imflawlezz/tty-buddy/hardware/schematics/tty-buddy/tty-buddy.kicad_sch

## KiCad design hardware/schematics/tty-buddy/tty-buddy.kicad_sch (2026-09-05)

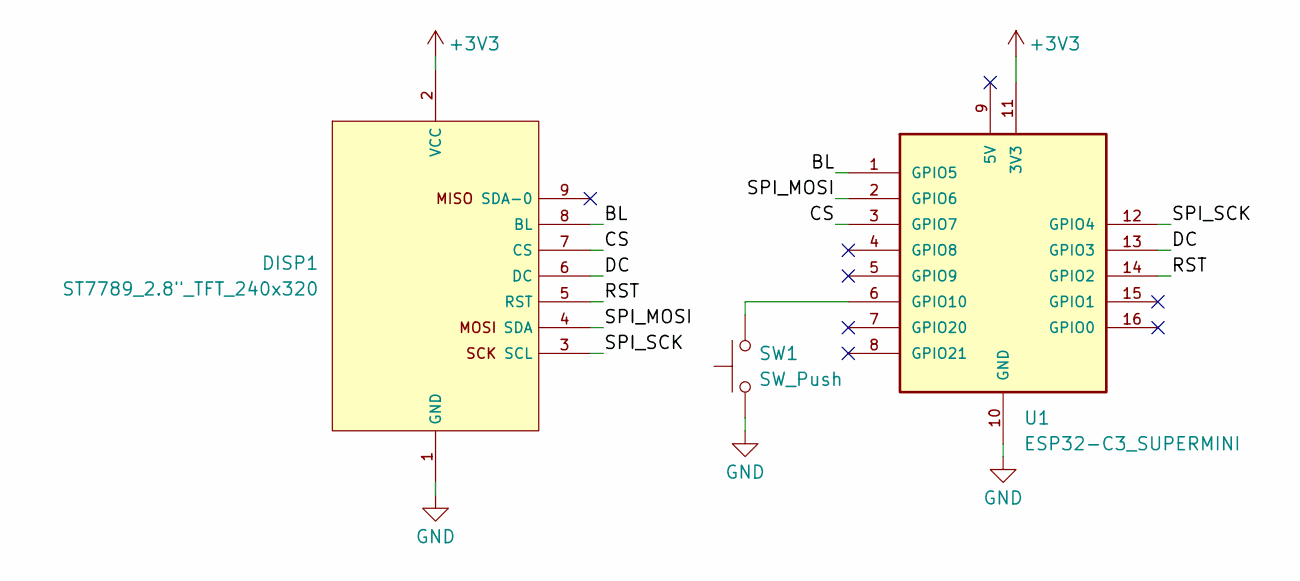
[picture p5: schematic tty-buddy.kicad_sch]

Parts:
DISP1: ST7789_2.8"_TFT_240x320
SW1: SW_Push
U1: ESP32-C3_SUPERMINI

Connections:
+3V3: DISP1.2 (VCC), U1.11 (3V3)
BL: DISP1.8 (BL), U1.1 (GPIO5)
CS: DISP1.7 (CS), U1.3 (GPIO7)
DC: DISP1.6 (DC), U1.13 (GPIO3)
GND: DISP1.1 (GND), SW1.1, U1.10 (GND)
unnamed: SW1.2, U1.6 (GPIO10)
RST: DISP1.5 (RST), U1.14 (GPIO2)
SPI_MOSI: DISP1.4 (SDA), U1.2 (GPIO6)
SPI_SCK: DISP1.3 (SCL), U1.12 (GPIO4)
