imflawlezz/tty-buddy/daemon/src/discover.rs

//! USB serial discovery (Linux sysfs + optional saved settings).

use std::fmt;
use std::fs;
use std::path::{Path, PathBuf};

use anyhow::Result;

use crate::settings::DaemonSettings;

pub const ESP_VID: u16 = 0x303A;
pub const ESP_PID_JTAG: u16 = 0x1001;

#[derive(Debug, Clone)]
pub struct SerialDevice {
    pub path: String,
    pub vid: Option<u16>,
    pub pid: Option<u16>,
    pub serial: Option<String>,
    pub product: Option<String>,
    pub manufacturer: Option<String>,
}

impl fmt::Display for SerialDevice {
    fn fmt(&self, f: &mut fmt::Formatter<'_>) -> fmt::Result {
        write!(f, "{}", self.path)?;
        match (self.vid, self.pid) {
            (Some(v), Some(p)) => write!(f, "  {:04x}:{:04x}", v, p)?,
            _ => write!(f, "  ????")?,
        }
        if let Some(ref m) = self.manufacturer {
            write!(f, "  {m}")?;
        }
        if let Some(ref p) = self.product {
            write!(f, "  {p}")?;
        }
        if let Some(ref s) = self.serial {
            write!(f, "  serial={s}")?;
        }
        if self.vid == Some(ESP_VID) {
            write!(f, "  [espressif]")?;
        }
        Ok(())
    }
}

fn read_hex_u16(path: &Path) -> Option<u16> {
    let s = fs::read_to_string(path).ok()?;
    u16::from_str_radix(s.trim(), 16).ok()
}

fn read_trim(path: &Path) -> Option<String> {
    let s = fs::read_to_string(path).ok()?;
    let t = s.trim().to_string();
    if t.is_empty() {
        None
    } else {
        Some(t)
    }
}

type UsbProps = (
    Option<u16>,
    Option<u16>,
    Option<String>,
    Option<String>,
    Option<String>,
);

fn usb_props_for_tty(tty_name: &str) -> UsbProps {
    // Walk sysfs parents until idVendor is found (USB device node).
    let mut cur = PathBuf::from(format!("/sys/class/tty/{tty_name}/device"));
    for _ in 0..8 {
        let vid_p = cur.join("idVendor");
        if vid_p.is_file() {
            return (
                read_hex_u16(&vid_p),
                read_hex_u16(&cur.join("idProduct")),
                read_trim(&cur.join("serial")),
                read_trim(&cur.join("product")),
                read_trim(&cur.join("manufacturer")),
            );
        }
        let parent = cur.join("..");
        let Ok(canon) = fs::canonicalize(&parent) else {
            break;
        };
        cur = canon;
    }
    (None, None, None, None, None)
}

fn push_stable_symlink(
    path: &str,
    out: &mut Vec<SerialDevice>,
    seen: &mut std::collections::HashSet<String>,
) {
    if !Path::new(path).exists() {
        return;
    }
    let real = fs::canonicalize(path)
        .map(|p| p.to_string_lossy().to_string())
        .unwrap_or_else(|_| path.to_string());
    if !seen.insert(real.clone()) {
        return;
    }
    let base = Path::new(&real)
        .file_name()
        .and_then(|s| s.to_str())
        .unwrap_or("");
    let (vid, pid, serial, product, manufacturer) = usb_props_for_tty(base);
    out.push(SerialDevice {
        path: path.to_string(),
        vid,
        pid,
        serial,
        product,
        manufacturer,
    });
}

pub fn list_serial_devices() -> Result<Vec<SerialDevice>> {
    let mut out = Vec::new();
    let mut seen = std::collections::HashSet::new();

    // Prefer udev stable names over raw ttyACM*/ttyUSB*.
    push_stable_symlink("/dev/tty-buddy", &mut out, &mut seen);
    if let Ok(paths) = glob_dev("/dev/tty-buddy-*") {
        let mut paths = paths;
        paths.sort();
        for path in paths {
            let s = path.to_string_lossy().to_string();
            push_stable_symlink(&s, &mut out, &mut seen);
        }
    }

    let mut nodes: Vec<PathBuf> = Vec::new();
    for pat in ["/dev/ttyACM*", "/dev/ttyUSB*"] {
        if let Ok(paths) = glob_dev(pat) {
            nodes.extend(paths);
        }
    }
    nodes.sort();
    for path in nodes {
        let s = path.to_string_lossy().to_string();
        let real = fs::canonicalize(&path)
            .map(|p| p.to_string_lossy().to_string())
            .unwrap_or_else(|_| s.clone());
        if !seen.insert(real.clone()) {
            continue;
        }
        let base = path.file_name().and_then(|x| x.to_str()).unwrap_or("");
        let (vid, pid, serial, product, manufacturer) = usb_props_for_tty(base);
        out.push(SerialDevice {
            path: s,
            vid,
            pid,
            serial,
            product,
            manufacturer,
        });
    }

    out.sort_by_key(|d| (if d.vid == Some(ESP_VID) { 0 } else { 1 }, d.path.clone()));
    Ok(out)
}

fn glob_dev(pattern: &str) -> Result<Vec<PathBuf>> {
    let dir = Path::new("/dev");
    let prefix = pattern.rsplit('/').next().unwrap_or("");
    let (pre, _) = prefix.split_once('*').unwrap_or((prefix, ""));
    let mut v = Vec::new();
    if let Ok(rd) = fs::read_dir(dir) {
        for e in rd.flatten() {
            let name = e.file_name();
            let n = name.to_string_lossy();
            if n.starts_with(pre) {
                v.push(e.path());
            }
        }
    }
    Ok(v)
}

pub fn resolve_device(settings: &DaemonSettings) -> Result<String> {
    let devices = list_serial_devices()?;
    pick_device(&devices, settings, |p| Path::new(p).exists())
        .ok_or_else(|| anyhow::anyhow!("no serial device available"))
}

/// Choose a device path from `devices` using settings; `path_exists` is injectable for tests.
pub(crate) fn pick_device(
    devices: &[SerialDevice],
    settings: &DaemonSettings,
    path_exists: impl Fn(&str) -> bool,
) -> Option<String> {
    if let Some(ref path) = settings.device_path {
        if path_exists(path) {
            return Some(path.clone());
        }
    }

    // Serial pin is fail-closed: never fall through to a different board.
    if let Some(ref ser) = settings.serial {
        let pool: Vec<_> = match (settings.vid, settings.pid) {
            (Some(vid), Some(pid)) => devices
                .iter()
                .filter(|d| d.vid == Some(vid) && d.pid == Some(pid))
                .collect(),
            _ => devices.iter().collect(),
        };
        return pool
            .into_iter()
            .find(|d| d.serial.as_deref() == Some(ser.as_str()))
            .map(|d| d.path.clone());
    }

    if let (Some(vid), Some(pid)) = (settings.vid, settings.pid) {
        let matches: Vec<_> = devices
            .iter()
            .filter(|d| d.vid == Some(vid) && d.pid == Some(pid))
            .collect();
        if matches.len() == 1 {
            return Some(matches[0].path.clone());
        }
        if let Some(d) = matches.first() {
            return Some(d.path.clone());
        }
    }

    let esp: Vec<_> = devices
        .iter()
        .filter(|d| d.vid == Some(ESP_VID) && d.pid == Some(ESP_PID_JTAG))
        .collect();
    if !esp.is_empty() {
        return Some(esp[0].path.clone());
    }
    if devices.len() == 1 {
        return Some(devices[0].path.clone());
    }
    if !devices.is_empty() {
        if let Some(d) = devices.iter().find(|d| d.path == "/dev/tty-buddy") {
            return Some(d.path.clone());
        }
        return Some(devices[0].path.clone());
    }
    None
}

#[cfg(test)]
mod tests {
    use super::*;

    fn dev(path: &str, vid: Option<u16>, pid: Option<u16>, serial: Option<&str>) -> SerialDevice {
        SerialDevice {
            path: path.into(),
            vid,
            pid,
            serial: serial.map(str::to_string),
            product: None,
            manufacturer: None,
        }
    }

    #[test]
    fn prefers_configured_path_when_present() {
        let settings = DaemonSettings {
            device_path: Some("/dev/custom".into()),
            ..DaemonSettings::default()
        };
        let devices = vec![dev("/dev/ttyACM0", Some(ESP_VID), Some(ESP_PID_JTAG), None)];
        let picked = pick_device(&devices, &settings, |p| p == "/dev/custom");
        assert_eq!(picked.as_deref(), Some("/dev/custom"));
    }

    #[test]
    fn matches_vid_pid_and_serial() {
        let settings = DaemonSettings {
            device_path: None,
            vid: Some(ESP_VID),
            pid: Some(ESP_PID_JTAG),
            serial: Some("ABC".into()),
            ..DaemonSettings::default()
        };
        let devices = vec![
            dev(
                "/dev/ttyACM0",
                Some(ESP_VID),
                Some(ESP_PID_JTAG),
                Some("ZZZ"),
            ),
            dev(
                "/dev/ttyACM1",
                Some(ESP_VID),
                Some(ESP_PID_JTAG),
                Some("ABC"),
            ),
        ];
        let picked = pick_device(&devices, &settings, |_| false);
        assert_eq!(picked.as_deref(), Some("/dev/ttyACM1"));
    }

    #[test]
    fn serial_unmatched_does_not_fall_through() {
        let settings = DaemonSettings {
            device_path: None,
            vid: Some(ESP_VID),
            pid: Some(ESP_PID_JTAG),
            serial: Some("MISSING".into()),
            ..DaemonSettings::default()
        };
        let devices = vec![
            dev(
                "/dev/ttyACM0",
                Some(ESP_VID),
                Some(ESP_PID_JTAG),
                Some("ZZZ"),
            ),
            dev(
                "/dev/ttyACM1",
                Some(ESP_VID),
                Some(ESP_PID_JTAG),
                Some("ABC"),
            ),
        ];
        assert_eq!(pick_device(&devices, &settings, |_| false), None);
    }

    #[test]
    fn falls_back_to_espressif_then_tty_buddy() {
        let settings = DaemonSettings {
            device_path: None,
            vid: None,
            pid: None,
            serial: None,
            ..DaemonSettings::default()
        };
        let devices = vec![
            dev("/dev/ttyUSB0", Some(0x1234), Some(0x5678), None),
            dev("/dev/ttyACM0", Some(ESP_VID), Some(ESP_PID_JTAG), None),
        ];
        assert_eq!(
            pick_device(&devices, &settings, |_| false).as_deref(),
            Some("/dev/ttyACM0")
        );

        let mixed = vec![
            dev("/dev/ttyUSB0", Some(0x1234), Some(0x5678), None),
            dev("/dev/tty-buddy", Some(0x1234), Some(0x5678), None),
        ];
        assert_eq!(
            pick_device(&mixed, &settings, |_| false).as_deref(),
            Some("/dev/tty-buddy")
        );
    }

    #[test]
    fn prefers_serial_suffixed_device_path() {
        let path = "/dev/tty-buddy-7C:DF:A1:12:34:56";
        let settings = DaemonSettings {
            device_path: Some(path.into()),
            serial: Some("7C:DF:A1:12:34:56".into()),
            ..DaemonSettings::default()
        };
        let devices = vec![
            dev(
                "/dev/tty-buddy",
                Some(ESP_VID),
                Some(ESP_PID_JTAG),
                Some("AA:BB"),
            ),
            dev(
                path,
                Some(ESP_VID),
                Some(ESP_PID_JTAG),
                Some("7C:DF:A1:12:34:56"),
            ),
        ];
        let picked = pick_device(&devices, &settings, |p| p == path);
        assert_eq!(picked.as_deref(), Some(path));
    }

    #[test]
    fn matches_serial_on_suffixed_symlink() {
        let settings = DaemonSettings {
            device_path: None,
            vid: Some(ESP_VID),
            pid: Some(ESP_PID_JTAG),
            serial: Some("7C:DF:A1:12:34:56".into()),
            ..DaemonSettings::default()
        };
        let devices = vec![
            dev(
                "/dev/tty-buddy",
                Some(ESP_VID),
                Some(ESP_PID_JTAG),
                Some("AA:BB:CC:DD:EE:FF"),
            ),
            dev(
                "/dev/tty-buddy-7C:DF:A1:12:34:56",
                Some(ESP_VID),
                Some(ESP_PID_JTAG),
                Some("7C:DF:A1:12:34:56"),
            ),
        ];
        assert_eq!(
            pick_device(&devices, &settings, |_| false).as_deref(),
            Some("/dev/tty-buddy-7C:DF:A1:12:34:56")
        );
    }
}
