imflawlezz/tty-buddy/daemon/src/metrics.rs

//! Live Linux host metrics for StatusSnap.

use std::collections::HashMap;
use std::fs;
use std::process::Command;
use std::time::{Duration, Instant};

use anyhow::Result;
use chrono::Local;

use crate::protocol::{
    StatusIface, StatusSnap, StatusSvc, ST_F_HAS_CPU, ST_F_HAS_DISK, ST_F_HAS_MEM, ST_F_HAS_TEMP,
    ST_SVC_ACTIVATING, ST_SVC_ACTIVE, ST_SVC_DEACTIVATING, ST_SVC_FAILED, ST_SVC_INACTIVE,
    ST_SVC_MAINTENANCE, ST_SVC_RELOADING, SVC_COUNT, SVC_NAME_LEN,
};
use crate::status_config::{IpMode, StatusUiConfig};

/// Cache TTL for `ip` / `systemctl` forks; `/proc` metrics still refresh ~1 Hz.
const SLOW_POLL_TTL: Duration = Duration::from_secs(3);

pub struct MetricsCollector {
    prev_cpu: Option<(u64, u64)>,
    prev_net: HashMap<String, (Instant, u64, u64)>,
    net_rates: HashMap<String, (u32, u32)>,
    iface_ips: HashMap<(String, IpMode), (Instant, String)>,
    services_cache: Option<(Instant, Option<Vec<String>>, Vec<StatusSvc>)>,
}

impl Default for MetricsCollector {
    fn default() -> Self {
        Self::new()
    }
}

impl MetricsCollector {
    pub fn new() -> Self {
        Self {
            prev_cpu: None,
            prev_net: HashMap::new(),
            net_rates: HashMap::new(),
            iface_ips: HashMap::new(),
            services_cache: None,
        }
    }

    pub fn sample(&mut self, cfg: &StatusUiConfig) -> Result<StatusSnap> {
        let mut snap = StatusSnap {
            style: cfg.style.clone(),
            ..Default::default()
        };

        let host = hostname();
        snap.hostname = host.split('.').next().unwrap_or(&host).to_string();

        let now = Local::now();
        snap.date = strftime_chrono(&cfg.date_format, &now);
        snap.time = strftime_chrono(&cfg.time_format, &now);

        if let Ok(load) = loadavg() {
            snap.load_x100 = [
                (load.0 * 100.0).round().clamp(0.0, 65535.0) as u16,
                (load.1 * 100.0).round().clamp(0.0, 65535.0) as u16,
                (load.2 * 100.0).round().clamp(0.0, 65535.0) as u16,
            ];
        }
        snap.uptime_sec = uptime_sec().unwrap_or(0);

        if let Some(cpu) = self.cpu_percent() {
            snap.flags |= ST_F_HAS_CPU;
            snap.cpu_pct = cpu.round().clamp(0.0, 100.0) as u8;
        }
        if let Some((used, total, pct)) = mem_info() {
            snap.flags |= ST_F_HAS_MEM;
            snap.mem_used_mb = used;
            snap.mem_total_mb = total;
            snap.mem_pct = pct;
        }
        if let Some((used, total, pct)) = swap_info() {
            snap.swap_used_mb = used;
            snap.swap_total_mb = total;
            snap.swap_pct = if total == 0 { 255 } else { pct };
        }
        if let Some((used, total, pct)) = disk_info(&cfg.disk_mount) {
            snap.flags |= ST_F_HAS_DISK;
            snap.disk_used_mb = used;
            snap.disk_total_mb = total;
            snap.disk_pct = pct;
        }
        if let Some(t10) = cpu_temp_c10() {
            snap.flags |= ST_F_HAS_TEMP;
            snap.cpu_temp_c10 = t10;
        }

        snap.ifaces = self.collect_ifaces(&cfg.interfaces);
        snap.services = self.collect_services_cached(cfg.services_filter.as_deref());

        Ok(snap)
    }

    fn cpu_percent(&mut self) -> Option<f32> {
        let (idle, total) = read_cpu_times()?;
        let out = if let Some((pi, pt)) = self.prev_cpu {
            let di = idle.saturating_sub(pi) as f64;
            let dt = total.saturating_sub(pt) as f64;
            if dt > 0.0 {
                Some((1.0 - di / dt) as f32 * 100.0)
            } else {
                None
            }
        } else {
            None
        };
        self.prev_cpu = Some((idle, total));
        out
    }

    fn iface_ip_cached(&mut self, name: &str, mode: IpMode) -> String {
        let key = (name.to_string(), mode);
        if let Some((t, ip)) = self.iface_ips.get(&key) {
            if t.elapsed() < SLOW_POLL_TTL {
                return ip.clone();
            }
        }
        let ip = iface_ip(name, mode).unwrap_or_default();
        self.iface_ips.insert(key, (Instant::now(), ip.clone()));
        ip
    }

    fn collect_services_cached(&mut self, filter: Option<&[String]>) -> Vec<StatusSvc> {
        let key = filter.map(|f| f.to_vec());
        if let Some((t, cached_key, svcs)) = &self.services_cache {
            if t.elapsed() < SLOW_POLL_TTL && cached_key == &key {
                return svcs.clone();
            }
        }
        let svcs = collect_services(filter);
        self.services_cache = Some((Instant::now(), key, svcs.clone()));
        svcs
    }

    fn collect_ifaces(&mut self, wanted: &[(String, IpMode)]) -> Vec<StatusIface> {
        if wanted.is_empty() {
            return Vec::new();
        }
        let stats = read_netdev();
        let now = Instant::now();
        let mut out = Vec::new();
        for (name, mode) in wanted.iter().take(16) {
            let (rx, tx) = stats.get(name).copied().unwrap_or((0, 0));
            if let Some((pt, prx, ptx)) = self.prev_net.get(name) {
                let dt = now.duration_since(*pt).as_secs_f64().max(0.001);
                let rbps = ((rx.saturating_sub(*prx)) as f64 / dt) as u32;
                let tbps = ((tx.saturating_sub(*ptx)) as f64 / dt) as u32;
                self.net_rates.insert(name.clone(), (rbps, tbps));
            }
            self.prev_net.insert(name.clone(), (now, rx, tx));
            let (rx_bps, tx_bps) = self.net_rates.get(name).copied().unwrap_or((0, 0));
            let ip = self.iface_ip_cached(name, *mode);
            out.push(StatusIface {
                name: name.clone(),
                ip,
                rx_bps,
                tx_bps,
            });
        }
        out
    }
}

fn hostname() -> String {
    fs::read_to_string("/etc/hostname")
        .map(|s| s.trim().to_string())
        .unwrap_or_else(|_| {
            Command::new("hostname")
                .output()
                .ok()
                .map(|o| String::from_utf8_lossy(&o.stdout).trim().to_string())
                .unwrap_or_else(|| "host".into())
        })
}

pub(crate) fn strftime_chrono(fmt: &str, t: &chrono::DateTime<Local>) -> String {
    // buddy.config date formats use C/Python-style % tokens; map the common subset to chrono.
    let mut out = String::new();
    let mut chars = fmt.chars().peekable();
    while let Some(c) = chars.next() {
        if c != '%' {
            out.push(c);
            continue;
        }
        let Some(spec) = chars.next() else {
            out.push('%');
            break;
        };
        let piece = match spec {
            'Y' => t.format("%Y").to_string(),
            'y' => t.format("%y").to_string(),
            'm' => t.format("%m").to_string(),
            'd' => t.format("%d").to_string(),
            'H' => t.format("%H").to_string(),
            'I' => t.format("%I").to_string(),
            'M' => t.format("%M").to_string(),
            'S' => t.format("%S").to_string(),
            'b' => t.format("%b").to_string(),
            'B' => t.format("%B").to_string(),
            'a' => t.format("%a").to_string(),
            'A' => t.format("%A").to_string(),
            'p' => t.format("%p").to_string(),
            '%' => "%".into(),
            other => format!("%{other}"),
        };
        out.push_str(&piece);
    }
    out
}

fn loadavg() -> Result<(f32, f32, f32)> {
    let s = fs::read_to_string("/proc/loadavg")?;
    let mut parts = s.split_whitespace();
    let a: f32 = parts.next().unwrap_or("0").parse()?;
    let b: f32 = parts.next().unwrap_or("0").parse()?;
    let c: f32 = parts.next().unwrap_or("0").parse()?;
    Ok((a, b, c))
}

fn uptime_sec() -> Result<u32> {
    let s = fs::read_to_string("/proc/uptime")?;
    let sec: f64 = s.split_whitespace().next().unwrap_or("0").parse()?;
    Ok(sec as u32)
}

fn read_cpu_times() -> Option<(u64, u64)> {
    let s = fs::read_to_string("/proc/stat").ok()?;
    let line = s.lines().next()?;
    if !line.starts_with("cpu ") {
        return None;
    }
    let nums: Vec<u64> = line
        .split_whitespace()
        .skip(1)
        .filter_map(|x| x.parse().ok())
        .collect();
    if nums.len() < 4 {
        return None;
    }
    let idle = nums[3] + nums.get(4).copied().unwrap_or(0); // idle + iowait
    let total: u64 = nums.iter().sum();
    Some((idle, total))
}

fn mem_info() -> Option<(u32, u32, u8)> {
    let s = fs::read_to_string("/proc/meminfo").ok()?;
    let mut total_kb = 0u64;
    let mut avail_kb = 0u64;
    for line in s.lines() {
        if line.starts_with("MemTotal:") {
            total_kb = line.split_whitespace().nth(1)?.parse().ok()?;
        } else if line.starts_with("MemAvailable:") {
            avail_kb = line.split_whitespace().nth(1)?.parse().ok()?;
        }
    }
    if total_kb == 0 {
        return None;
    }
    let used_kb = total_kb.saturating_sub(avail_kb);
    let pct = ((used_kb as f64 / total_kb as f64) * 100.0).round() as u8;
    Some((
        (used_kb / 1024) as u32,
        (total_kb / 1024) as u32,
        pct.min(100),
    ))
}

fn swap_info() -> Option<(u32, u32, u8)> {
    let s = fs::read_to_string("/proc/meminfo").ok()?;
    let mut total_kb = 0u64;
    let mut free_kb = 0u64;
    for line in s.lines() {
        if line.starts_with("SwapTotal:") {
            total_kb = line.split_whitespace().nth(1)?.parse().ok()?;
        } else if line.starts_with("SwapFree:") {
            free_kb = line.split_whitespace().nth(1)?.parse().ok()?;
        }
    }
    if total_kb == 0 {
        return Some((0, 0, 255));
    }
    let used_kb = total_kb.saturating_sub(free_kb);
    let pct = ((used_kb as f64 / total_kb as f64) * 100.0).round() as u8;
    Some((
        (used_kb / 1024) as u32,
        (total_kb / 1024) as u32,
        pct.min(100),
    ))
}

fn disk_info(mount: &str) -> Option<(u32, u32, u8)> {
    let mut st: libc::statvfs = unsafe { std::mem::zeroed() };
    let c = std::ffi::CString::new(mount).ok()?;
    let rc = unsafe { libc::statvfs(c.as_ptr(), &mut st) };
    if rc != 0 {
        return None;
    }
    let frsize = st.f_frsize as u64;
    let total = (st.f_blocks as u64).saturating_mul(frsize);
    let avail = (st.f_bavail as u64).saturating_mul(frsize);
    let used = total.saturating_sub(avail);
    if total == 0 {
        return None;
    }
    let pct = ((used as f64 / total as f64) * 100.0).round() as u8;
    Some((
        (used / (1024 * 1024)) as u32,
        (total / (1024 * 1024)) as u32,
        pct.min(100),
    ))
}

fn cpu_temp_c10() -> Option<i16> {
    let zones = fs::read_dir("/sys/class/thermal").ok()?;
    let mut best: Option<i64> = None;
    for e in zones.flatten() {
        let path = e.path();
        let name = path.file_name()?.to_string_lossy().to_string();
        if !name.starts_with("thermal_zone") {
            continue;
        }
        let typ = fs::read_to_string(path.join("type")).ok()?;
        let typ = typ.trim();
        let temp: i64 = fs::read_to_string(path.join("temp"))
            .ok()?
            .trim()
            .parse()
            .ok()?;
        if typ.contains("x86_pkg") || typ.contains("cpu") || typ.contains("soc") {
            return Some((temp / 100) as i16); // millidegree → c10
        }
        if best.is_none() {
            best = Some(temp);
        }
    }
    best.map(|t| (t / 100) as i16)
}

fn read_netdev() -> HashMap<String, (u64, u64)> {
    let Ok(s) = fs::read_to_string("/proc/net/dev") else {
        return HashMap::new();
    };
    parse_netdev_table(&s)
}

pub(crate) fn parse_netdev_table(s: &str) -> HashMap<String, (u64, u64)> {
    let mut map = HashMap::new();
    for line in s.lines().skip(2) {
        let line = line.trim();
        let Some((name, rest)) = line.split_once(':') else {
            continue;
        };
        let name = name.trim().to_string();
        let cols: Vec<&str> = rest.split_whitespace().collect();
        if cols.len() < 9 {
            continue;
        }
        let rx: u64 = cols[0].parse().unwrap_or(0);
        let tx: u64 = cols[8].parse().unwrap_or(0);
        map.insert(name, (rx, tx));
    }
    map
}

fn iface_ip(name: &str, mode: IpMode) -> Option<String> {
    match mode {
        IpMode::V4 => iface_ip_family(name, false),
        IpMode::V6 => iface_ip_family(name, true),
        IpMode::Auto => iface_ip_family(name, false).or_else(|| iface_ip_family(name, true)),
    }
}

fn iface_ip_family(name: &str, v6: bool) -> Option<String> {
    let out = Command::new("ip")
        .args([
            "-o",
            if v6 { "-6" } else { "-4" },
            "addr",
            "show",
            "dev",
            name,
        ])
        .output()
        .ok()?;
    let text = String::from_utf8_lossy(&out.stdout);
    let mut link_local: Option<String> = None;
    for line in text.lines() {
        let mut parts = line.split_whitespace();
        while let Some(p) = parts.next() {
            if p == "inet" || p == "inet6" {
                if let Some(addr) = parts.next() {
                    let addr = addr.split('/').next().unwrap_or(addr).to_string();
                    if v6 && addr.starts_with("fe80:") {
                        if link_local.is_none() {
                            link_local = Some(addr);
                        }
                        continue;
                    }
                    return Some(addr);
                }
            }
        }
    }
    link_local
}

pub(crate) fn normalize_svc_status(active: &str) -> u8 {
    match active.trim().to_ascii_lowercase().as_str() {
        "active" => ST_SVC_ACTIVE,
        "failed" => ST_SVC_FAILED,
        "inactive" => ST_SVC_INACTIVE,
        "activating" => ST_SVC_ACTIVATING,
        "deactivating" => ST_SVC_DEACTIVATING,
        "reloading" => ST_SVC_RELOADING,
        "maintenance" => ST_SVC_MAINTENANCE,
        _ => ST_SVC_MAINTENANCE,
    }
}

fn collect_services(filter: Option<&[String]>) -> Vec<StatusSvc> {
    match filter {
        Some(names) => collect_filtered_services(names),
        None => {
            let out = Command::new("systemctl")
                .args([
                    "list-units",
                    "--type=service",
                    "--all",
                    "--no-legend",
                    "--no-pager",
                    "--plain",
                ])
                .output();
            let Ok(out) = out else {
                return Vec::new();
            };
            let text = String::from_utf8_lossy(&out.stdout);
            parse_systemctl_services(&text, None)
        }
    }
}

/// `list-units --all` omits unloaded stopped units; batch-query with `is-active`.
fn collect_filtered_services(filter: &[String]) -> Vec<StatusSvc> {
    let units: Vec<String> = filter
        .iter()
        .take(SVC_COUNT)
        .filter_map(|entry| {
            let unit = if entry.ends_with(".service") {
                entry.clone()
            } else {
                format!("{entry}.service")
            };
            let name = unit.trim_end_matches(".service");
            if name.ends_with('@') {
                None
            } else {
                Some(unit)
            }
        })
        .collect();
    if units.is_empty() {
        return Vec::new();
    }

    let states = match Command::new("systemctl")
        .arg("is-active")
        .args(&units)
        .output()
    {
        Ok(out) => String::from_utf8_lossy(&out.stdout)
            .lines()
            .map(|s| s.trim().to_string())
            .collect::<Vec<_>>(),
        Err(_) => Vec::new(),
    };

    services_from_is_active(&units, &states)
}

pub(crate) fn services_from_is_active(units: &[String], states: &[String]) -> Vec<StatusSvc> {
    units
        .iter()
        .enumerate()
        .map(|(i, unit)| {
            let name = unit.trim_end_matches(".service");
            let status = states
                .get(i)
                .map(|s| normalize_svc_status(s))
                .unwrap_or(ST_SVC_MAINTENANCE);
            StatusSvc {
                name: name.chars().take(SVC_NAME_LEN).collect(),
                status,
            }
        })
        .collect()
}

pub(crate) fn parse_systemctl_services(text: &str, filter: Option<&[String]>) -> Vec<StatusSvc> {
    let mut services = Vec::new();
    for line in text.lines() {
        let cols: Vec<&str> = line.split_whitespace().collect();
        if cols.len() < 4 {
            continue;
        }
        let unit = cols[0];
        if !unit.ends_with(".service") {
            continue;
        }
        let name = unit.trim_end_matches(".service");
        if name.ends_with('@') {
            continue;
        }
        if let Some(f) = filter {
            if !f.iter().any(|x| x == name || x == unit) {
                continue;
            }
        }
        // systemctl --plain: UNIT LOAD ACTIVE SUB …
        let active = cols[2];
        services.push(StatusSvc {
            name: name.chars().take(SVC_NAME_LEN).collect(),
            status: normalize_svc_status(active),
        });
        if filter.is_some() && services.len() >= SVC_COUNT {
            break;
        }
    }
    // Unfiltered: failed/transitioning first, then truncate to wire capacity.
    if filter.is_none() {
        services.sort_by_key(|s| match s.status {
            ST_SVC_FAILED => 0,
            ST_SVC_ACTIVATING | ST_SVC_RELOADING | ST_SVC_DEACTIVATING => 1,
            ST_SVC_ACTIVE => 2,
            ST_SVC_INACTIVE => 3,
            _ => 4,
        });
        services.truncate(SVC_COUNT);
    }
    services
}

#[cfg(test)]
mod tests {
    use super::*;
    use chrono::TimeZone;

    #[test]
    fn svc_status_mapping() {
        assert_eq!(normalize_svc_status("active"), ST_SVC_ACTIVE);
        assert_eq!(normalize_svc_status("FAILED"), ST_SVC_FAILED);
        assert_eq!(normalize_svc_status(" inactive "), ST_SVC_INACTIVE);
        assert_eq!(normalize_svc_status("activating"), ST_SVC_ACTIVATING);
        assert_eq!(normalize_svc_status("deactivating"), ST_SVC_DEACTIVATING);
        assert_eq!(normalize_svc_status("reloading"), ST_SVC_RELOADING);
        assert_eq!(normalize_svc_status("maintenance"), ST_SVC_MAINTENANCE);
        assert_eq!(normalize_svc_status("weird"), ST_SVC_MAINTENANCE);
    }

    #[test]
    fn strftime_common_tokens() {
        let t = Local
            .with_ymd_and_hms(2026, 9, 8, 15, 4, 5)
            .single()
            .unwrap();
        assert_eq!(strftime_chrono("%Y-%m-%d", &t), "2026-09-08");
        assert_eq!(strftime_chrono("%d-%m-%Y", &t), "08-09-2026");
        assert_eq!(strftime_chrono("%H:%M:%S", &t), "15:04:05");
        assert_eq!(strftime_chrono("%%", &t), "%");
        assert_eq!(strftime_chrono("plain", &t), "plain");
    }

    #[test]
    fn netdev_table_parses_rx_tx() {
        let table = "\
Inter-|   Receive                                                |  Transmit
 face |bytes    packets errs drop fifo frame compressed multicast|bytes    packets errs drop fifo colls carrier compressed
  eth0: 1000 1 0 0 0 0 0 0 2000 2 0 0 0 0 0 0
 wlan0: 42 0 0 0 0 0 0 0 7 0 0 0 0 0 0 0
";
        let map = parse_netdev_table(table);
        assert_eq!(map.get("eth0"), Some(&(1000, 2000)));
        assert_eq!(map.get("wlan0"), Some(&(42, 7)));
    }

    #[test]
    fn systemctl_services_filter_and_sort() {
        let text = "\
ssh.service            loaded active   running OpenSSH
cron.service           loaded inactive dead    Regular
broken.service         loaded failed   failed  Boom
tmpl@.service          loaded active   running skip template
notaservice.target     loaded active   running ignore
docker.service         loaded activating start Docker
";
        let all = parse_systemctl_services(text, None);
        assert_eq!(all[0].name, "broken");
        assert_eq!(all[0].status, ST_SVC_FAILED);
        assert!(all.iter().any(|s| s.name == "docker"));
        assert!(!all
            .iter()
            .any(|s| s.name.ends_with('@') || s.name == "notaservice"));

        let filter = vec!["ssh".into(), "cron.service".into()];
        let filtered = parse_systemctl_services(text, Some(&filter));
        assert_eq!(filtered.len(), 2);
        assert!(filtered.iter().any(|s| s.name == "ssh"));
        assert!(filtered.iter().any(|s| s.name == "cron"));
        assert_eq!(
            filtered.iter().find(|s| s.name == "cron").unwrap().status,
            ST_SVC_INACTIVE
        );
    }

    #[test]
    fn systemctl_unfiltered_prioritizes_late_failed() {
        let mut lines = Vec::new();
        for i in 0..100 {
            lines.push(format!("svc{i}.service loaded active running x"));
        }
        lines.push("zzz-late.service loaded failed failed Boom".into());
        let text = lines.join("\n");
        let all = parse_systemctl_services(&text, None);
        assert_eq!(all.len(), SVC_COUNT);
        assert_eq!(all[0].name, "zzz-late");
        assert_eq!(all[0].status, ST_SVC_FAILED);
    }

    #[test]
    fn systemctl_truncates_long_names() {
        let long = format!("{}.service loaded active running x", "a".repeat(60));
        let svcs = parse_systemctl_services(&long, None);
        assert_eq!(svcs.len(), 1);
        assert_eq!(svcs[0].name.len(), SVC_NAME_LEN);
    }

    #[test]
    fn filtered_services_zip_is_active_lines() {
        let units = vec![
            "ssh.service".into(),
            "cron.service".into(),
            "gone.service".into(),
        ];
        let states = vec!["active".into(), "inactive".into()];
        let svcs = services_from_is_active(&units, &states);
        assert_eq!(svcs.len(), 3);
        assert_eq!(svcs[0].name, "ssh");
        assert_eq!(svcs[0].status, ST_SVC_ACTIVE);
        assert_eq!(svcs[1].name, "cron");
        assert_eq!(svcs[1].status, ST_SVC_INACTIVE);
        assert_eq!(svcs[2].name, "gone");
        assert_eq!(svcs[2].status, ST_SVC_MAINTENANCE);
    }
}
