imflawlezz/tty-buddy/daemon/src/protocol.rs

//! Wire protocol: CRC frames and StatusSnap v13.

pub const COLS: usize = 53;
pub const ROWS: usize = 30;
pub const CELLS: usize = COLS * ROWS;
pub const PAYLOAD_LEN: usize = CELLS * 3; // 4770
pub const FRAME_LEN: usize = 4 + 4 + PAYLOAD_LEN + 2; // 4780

pub const FRAME_MAGIC: [u8; 4] = [0xAA, 0x55, 0xA5, 0x5A];
pub const FRAME_ACK: u8 = 0x06;
pub const FRAME_NAK: u8 = 0x15;
pub const DEV_MODE_TOGGLE: u8 = 0x12;
pub const DEV_OSD_BRIGHT: u8 = 0x13; // +1 byte: 0=auto, 1..6
pub const DEV_OSD_SLEEP: u8 = 0x14; // +1 byte: 0=never, 1..6

pub const FLAG_CURSOR_VISIBLE: u8 = 0x01;
pub const FLAG_CURSOR_ON: u8 = 0x02;
pub const FLAG_ACTIVITY: u8 = 0x04;
pub const FLAG_STYLE: u8 = 0x10;
pub const FLAG_STATUS: u8 = 0x20;
pub const FLAG_BYE: u8 = 0x80;

pub const STATUS_VER: u8 = 13;
pub const STATUS_SNAP_LEN: usize = 4466;
pub const STYLE_LEN: usize = 60;
pub const IFACE_COUNT: usize = 16;
pub const SVC_COUNT: usize = 80;
pub const SVC_NAME_LEN: usize = 40;

pub const ST_F_HAS_TEMP: u8 = 0x02;
pub const ST_F_HAS_CPU: u8 = 0x20;
pub const ST_F_HAS_MEM: u8 = 0x40;
pub const ST_F_HAS_DISK: u8 = 0x80;

pub const ST_SVC_FAILED: u8 = 0;
pub const ST_SVC_ACTIVE: u8 = 1;
pub const ST_SVC_DEACTIVATING: u8 = 2;
pub const ST_SVC_ACTIVATING: u8 = 3;
pub const ST_SVC_INACTIVE: u8 = 4;
pub const ST_SVC_MAINTENANCE: u8 = 5;
pub const ST_SVC_RELOADING: u8 = 6;

pub const SEC_NONE: u8 = 0xFF;
pub const SEC_UPTIME: u8 = 1;
pub const SEC_SWAP: u8 = 2;
pub const SEC_LOAD: u8 = 3;

pub const METER_OFF: u8 = 0;
pub const METER_ON: u8 = 1;

pub const AL_CPU: u8 = 1 << 0;
pub const AL_MEM: u8 = 1 << 1;
pub const AL_DISK: u8 = 1 << 2;
pub const AL_TEMP: u8 = 1 << 3;
pub const AL_SVC_FAILED: u8 = 1 << 4;
pub const AL_SVC_INACTIVE: u8 = 1 << 5;

pub const OSD_F_DISMISS_ON_TAP: u8 = 1 << 0;
pub const OSD_F_AUTO_BRIGHT: u8 = 1 << 1;
pub const OSD_F_WAKE_ON_ALERT: u8 = 1 << 2;

pub fn crc16_ccitt(data: &[u8]) -> u16 {
    let mut crc: u16 = 0xFFFF;
    for &b in data {
        crc ^= (b as u16) << 8;
        for _ in 0..8 {
            if crc & 0x8000 != 0 {
                crc = (crc << 1) ^ 0x1021;
            } else {
                crc <<= 1;
            }
        }
    }
    crc
}

pub fn build_frame(seq: u8, cx: u8, cy: u8, flags: u8, payload: &[u8; PAYLOAD_LEN]) -> Vec<u8> {
    let hdr = [seq, cx, cy, flags];
    let mut crc_buf = Vec::with_capacity(4 + PAYLOAD_LEN);
    crc_buf.extend_from_slice(&hdr);
    crc_buf.extend_from_slice(payload);
    let crc = crc16_ccitt(&crc_buf);
    let mut out = Vec::with_capacity(FRAME_LEN);
    out.extend_from_slice(&FRAME_MAGIC);
    out.push(seq);
    out.push(cx);
    out.push(cy);
    out.push(flags);
    out.extend_from_slice(payload);
    out.push((crc >> 8) as u8);
    out.push((crc & 0xFF) as u8);
    let _ = hdr;
    out
}

#[derive(Clone, Debug)]
pub struct StatusStyle {
    pub label_c: u16,
    pub bg_c: u16,
    pub host_c: u16,
    pub date_c: u16,
    pub time_c: u16,
    pub level_ok: u16,
    pub level_warn: u16,
    pub level_crit: u16,
    pub hero_cpu_c: u16,
    pub hero_mem_c: u16,
    pub hero_disk_c: u16,
    pub meter_mode: u8,
    pub warn_at: u8,
    pub crit_at: u8,
    pub sec_left: u8,
    pub sec_right: u8,
    pub sec_left_c: u16,
    pub sec_right_c: u16,
    pub svc_active: u16,
    pub svc_failed: u16,
    pub svc_deactivating: u16,
    pub svc_activating: u16,
    pub svc_reloading: u16,
    pub svc_inactive: u16,
    pub svc_maintenance: u16,
    pub alert_bg_c: u16,
    pub alert_fg_c: u16,
    /// 0 = while problem active; N = max seconds if text unchanged.
    pub alert_hold_sec: u8,
    /// `AL_*` bits; 0 = off.
    pub alert_mask: u8,
    pub alert_temp_c: u8,
    /// Brightness step 1..6, or 0 = AUTO (see `OSD_F_AUTO_BRIGHT`).
    pub osd_default_bright_pct: u8,
    /// Sleep: 0 = never, 1..6 = level (device maps to seconds).
    pub osd_sleep_timeout_s: u16,
    /// `OSD_F_*` bits; applied live with bright/sleep fields.
    pub osd_flags: u8,
    /// AUTO daytime brightness step 1..6 (pct name kept for wire layout).
    pub osd_auto_day_pct: u8,
    /// AUTO nighttime brightness step 1..6.
    pub osd_auto_night_pct: u8,
    pub osd_auto_day_hour: u8,
    pub osd_auto_night_hour: u8,
}

impl Default for StatusStyle {
    fn default() -> Self {
        Self {
            label_c: rgb565(0x88, 0x88, 0x88),
            bg_c: 0,
            host_c: 0xFFFF,
            date_c: rgb565(0x88, 0x88, 0x88),
            time_c: 0xFFFF,
            level_ok: rgb565(0x33, 0xAA, 0x33),
            level_warn: rgb565(0xCC, 0xCC, 0x33),
            level_crit: rgb565(0xCC, 0x33, 0x33),
            hero_cpu_c: 0xFFFF,
            hero_mem_c: 0xFFFF,
            hero_disk_c: 0xFFFF,
            meter_mode: METER_ON,
            warn_at: 60,
            crit_at: 90,
            sec_left: SEC_NONE,
            sec_right: SEC_NONE,
            sec_left_c: 0xFFFF,
            sec_right_c: 0xFFFF,
            svc_active: rgb565(0x33, 0xAA, 0x33),
            svc_failed: rgb565(0xCC, 0x33, 0x33),
            svc_deactivating: rgb565(0xCC, 0xAA, 0x33),
            svc_activating: rgb565(0x33, 0x99, 0xCC),
            svc_reloading: rgb565(0x33, 0x99, 0xCC),
            svc_inactive: rgb565(0x88, 0x88, 0x88),
            svc_maintenance: rgb565(0x88, 0x88, 0x88),
            alert_bg_c: rgb565(0x99, 0x00, 0x00),
            alert_fg_c: 0xFFFF,
            alert_hold_sec: 0,
            alert_mask: 0,
            alert_temp_c: 80,
            osd_default_bright_pct: 4,
            osd_sleep_timeout_s: 4,
            osd_flags: OSD_F_DISMISS_ON_TAP | OSD_F_WAKE_ON_ALERT,
            osd_auto_day_pct: 5,
            osd_auto_night_pct: 2,
            osd_auto_day_hour: 7,
            osd_auto_night_hour: 21,
        }
    }
}

impl StatusStyle {
    pub fn pack(&self) -> [u8; STYLE_LEN] {
        let mut b = [0u8; STYLE_LEN];
        let mut o = 0usize;
        let put_u16 = |b: &mut [u8], o: &mut usize, v: u16| {
            b[*o..*o + 2].copy_from_slice(&v.to_le_bytes());
            *o += 2;
        };
        for v in [
            self.label_c,
            self.bg_c,
            self.host_c,
            self.date_c,
            self.time_c,
            self.level_ok,
            self.level_warn,
            self.level_crit,
            self.hero_cpu_c,
            self.hero_mem_c,
            self.hero_disk_c,
        ] {
            put_u16(&mut b, &mut o, v);
        }
        b[o] = self.meter_mode;
        b[o + 1] = self.warn_at;
        b[o + 2] = self.crit_at;
        b[o + 3] = self.sec_left;
        b[o + 4] = self.sec_right;
        o += 5;
        for v in [
            self.sec_left_c,
            self.sec_right_c,
            self.svc_active,
            self.svc_failed,
            self.svc_deactivating,
            self.svc_activating,
            self.svc_reloading,
            self.svc_inactive,
            self.svc_maintenance,
            self.alert_bg_c,
            self.alert_fg_c,
        ] {
            put_u16(&mut b, &mut o, v);
        }
        b[o] = self.alert_hold_sec;
        b[o + 1] = self.alert_mask;
        b[o + 2] = self.alert_temp_c;
        o += 3;
        b[o] = self.osd_default_bright_pct;
        o += 1;
        put_u16(&mut b, &mut o, self.osd_sleep_timeout_s);
        b[o] = self.osd_flags;
        b[o + 1] = self.osd_auto_day_pct;
        b[o + 2] = self.osd_auto_night_pct;
        b[o + 3] = self.osd_auto_day_hour;
        b[o + 4] = self.osd_auto_night_hour;
        o += 5;
        debug_assert_eq!(o, STYLE_LEN);
        b
    }
}

#[derive(Clone, Debug, Default)]
pub struct StatusIface {
    pub name: String,
    pub ip: String,
    pub rx_bps: u32,
    pub tx_bps: u32,
}

#[derive(Clone, Debug, Default)]
pub struct StatusSvc {
    pub name: String,
    pub status: u8,
}

#[derive(Clone, Debug)]
pub struct StatusSnap {
    pub flags: u8,
    pub style: StatusStyle,
    pub hostname: String,
    pub date: String,
    pub time: String,
    pub load_x100: [u16; 3],
    pub uptime_sec: u32,
    pub cpu_pct: u8,
    pub mem_pct: u8,
    pub disk_pct: u8,
    pub swap_pct: u8,
    pub mem_used_mb: u32,
    pub mem_total_mb: u32,
    pub disk_used_mb: u32,
    pub disk_total_mb: u32,
    pub swap_used_mb: u32,
    pub swap_total_mb: u32,
    pub cpu_temp_c10: i16,
    pub ifaces: Vec<StatusIface>,
    pub services: Vec<StatusSvc>,
}

impl Default for StatusSnap {
    fn default() -> Self {
        Self {
            flags: 0,
            style: StatusStyle::default(),
            hostname: String::new(),
            date: String::new(),
            time: String::new(),
            load_x100: [0; 3],
            uptime_sec: 0,
            cpu_pct: 255,
            mem_pct: 255,
            disk_pct: 255,
            swap_pct: 255,
            mem_used_mb: 0,
            mem_total_mb: 0,
            disk_used_mb: 0,
            disk_total_mb: 0,
            swap_used_mb: 0,
            swap_total_mb: 0,
            cpu_temp_c10: 0x7FFF,
            ifaces: Vec::new(),
            services: Vec::new(),
        }
    }
}

fn pad_str(s: &str, n: usize) -> Vec<u8> {
    let mut raw = s.as_bytes().to_vec();
    if raw.len() > n {
        raw.truncate(n);
        while std::str::from_utf8(&raw).is_err() {
            raw.pop();
        }
    }
    raw.resize(n, 0);
    raw
}

impl StatusSnap {
    pub fn pack(&self) -> [u8; STATUS_SNAP_LEN] {
        let mut out = [0u8; STATUS_SNAP_LEN];
        let mut o = 0usize;
        let put = |out: &mut [u8], o: &mut usize, bytes: &[u8]| {
            out[*o..*o + bytes.len()].copy_from_slice(bytes);
            *o += bytes.len();
        };
        put(&mut out, &mut o, b"TBST");
        put(&mut out, &mut o, &[STATUS_VER, self.flags]);
        put(&mut out, &mut o, &self.style.pack());
        put(&mut out, &mut o, &pad_str(&self.hostname, 24));
        put(&mut out, &mut o, &pad_str(&self.date, 20));
        put(&mut out, &mut o, &pad_str(&self.time, 12));
        for v in self.load_x100 {
            put(&mut out, &mut o, &v.to_le_bytes());
        }
        put(&mut out, &mut o, &self.uptime_sec.to_le_bytes());
        put(
            &mut out,
            &mut o,
            &[self.cpu_pct, self.mem_pct, self.disk_pct, self.swap_pct],
        );
        for v in [
            self.mem_used_mb,
            self.mem_total_mb,
            self.disk_used_mb,
            self.disk_total_mb,
            self.swap_used_mb,
            self.swap_total_mb,
        ] {
            put(&mut out, &mut o, &v.to_le_bytes());
        }
        put(&mut out, &mut o, &self.cpu_temp_c10.to_le_bytes());

        for i in 0..IFACE_COUNT {
            let iface = self.ifaces.get(i);
            let name = iface.map(|x| x.name.as_str()).unwrap_or("");
            let ip = iface.map(|x| x.ip.as_str()).unwrap_or("");
            let rx = iface.map(|x| x.rx_bps).unwrap_or(0);
            let tx = iface.map(|x| x.tx_bps).unwrap_or(0);
            put(&mut out, &mut o, &pad_str(name, 16));
            put(&mut out, &mut o, &pad_str(ip, 40));
            put(&mut out, &mut o, &rx.to_le_bytes());
            put(&mut out, &mut o, &tx.to_le_bytes());
        }
        for i in 0..SVC_COUNT {
            let svc = self.services.get(i);
            let name = svc.map(|x| x.name.as_str()).unwrap_or("");
            let st = svc.map(|x| x.status).unwrap_or(0);
            put(&mut out, &mut o, &pad_str(name, SVC_NAME_LEN));
            put(&mut out, &mut o, &[if name.is_empty() { 0 } else { st }]);
        }
        debug_assert_eq!(o, STATUS_SNAP_LEN);
        out
    }

    pub fn to_payload(&self) -> [u8; PAYLOAD_LEN] {
        let mut payload = [0u8; PAYLOAD_LEN];
        let snap = self.pack();
        payload[..STATUS_SNAP_LEN].copy_from_slice(&snap);
        payload
    }
}

pub fn rgb565(r: u8, g: u8, b: u8) -> u16 {
    (((r as u16) & 0xF8) << 8) | (((g as u16) & 0xFC) << 3) | ((b as u16) >> 3)
}

pub fn parse_hex_color(s: &str, default: u16) -> u16 {
    let t = s.trim();
    if t.is_empty() {
        return default;
    }
    let h = t.strip_prefix('#').unwrap_or(t);
    let h = if h.len() == 3 {
        format!(
            "{}{}{}{}{}{}",
            h.chars().next().unwrap(),
            h.chars().next().unwrap(),
            h.chars().nth(1).unwrap(),
            h.chars().nth(1).unwrap(),
            h.chars().nth(2).unwrap(),
            h.chars().nth(2).unwrap()
        )
    } else {
        h.to_string()
    };
    if h.len() != 6 {
        return default;
    }
    let Ok(r) = u8::from_str_radix(&h[0..2], 16) else {
        return default;
    };
    let Ok(g) = u8::from_str_radix(&h[2..4], 16) else {
        return default;
    };
    let Ok(b) = u8::from_str_radix(&h[4..6], 16) else {
        return default;
    };
    rgb565(r, g, b)
}

#[cfg(test)]
mod tests {
    use super::*;

    #[test]
    fn pad_str_truncates_on_utf8_boundary() {
        let p = pad_str("aé", 2);
        assert_eq!(p.len(), 2);
        assert_eq!(&p[..1], b"a");
        assert_eq!(p[1], 0);

        let p2 = pad_str("日本語", 4);
        assert_eq!(p2.len(), 4);
        assert_eq!(&p2[..3], "日".as_bytes());
        assert_eq!(p2[3], 0);
        assert!(std::str::from_utf8(&p2[..3]).is_ok());
    }

    #[test]
    fn sizes() {
        assert_eq!(PAYLOAD_LEN, 4770);
        assert_eq!(FRAME_LEN, 4780);
        assert_eq!(STATUS_SNAP_LEN, 4466);
        assert_eq!(STYLE_LEN, 60);
        assert_eq!(StatusStyle::default().pack().len(), 60);
        assert_eq!(StatusSnap::default().pack().len(), 4466);
    }

    #[test]
    fn crc16_empty_and_known() {
        assert_eq!(crc16_ccitt(&[]), 0xFFFF);
        // CRC-CCITT (init 0xFFFF, poly 0x1021) over "123456789"
        assert_eq!(crc16_ccitt(b"123456789"), 0x29B1);
    }

    #[test]
    fn build_frame_layout_and_crc() {
        let payload = [0u8; PAYLOAD_LEN];
        let frame = build_frame(7, 10, 20, FLAG_STATUS, &payload);
        assert_eq!(frame.len(), FRAME_LEN);
        assert_eq!(&frame[0..4], &FRAME_MAGIC);
        assert_eq!(frame[4], 7);
        assert_eq!(frame[5], 10);
        assert_eq!(frame[6], 20);
        assert_eq!(frame[7], FLAG_STATUS);
        let mut crc_buf = Vec::with_capacity(4 + PAYLOAD_LEN);
        crc_buf.extend_from_slice(&[7, 10, 20, FLAG_STATUS]);
        crc_buf.extend_from_slice(&payload);
        let crc = crc16_ccitt(&crc_buf);
        assert_eq!(frame[FRAME_LEN - 2], (crc >> 8) as u8);
        assert_eq!(frame[FRAME_LEN - 1], (crc & 0xFF) as u8);
    }

    #[test]
    fn rgb565_and_hex_colors() {
        assert_eq!(rgb565(0xFF, 0x00, 0x00), 0xF800);
        assert_eq!(rgb565(0x00, 0xFF, 0x00), 0x07E0);
        assert_eq!(rgb565(0x00, 0x00, 0xFF), 0x001F);
        assert_eq!(parse_hex_color("#F00", 0), rgb565(0xFF, 0x00, 0x00));
        assert_eq!(parse_hex_color("#00FF00", 0), rgb565(0x00, 0xFF, 0x00));
        assert_eq!(parse_hex_color("888888", 1), rgb565(0x88, 0x88, 0x88));
        assert_eq!(parse_hex_color("", 0x1234), 0x1234);
        assert_eq!(parse_hex_color("nope", 0xABCD), 0xABCD);
        assert_eq!(parse_hex_color("#12", 9), 9);
    }

    #[test]
    fn style_pack_le_fields() {
        let st = StatusStyle {
            label_c: 0xABCD,
            warn_at: 42,
            crit_at: 77,
            meter_mode: METER_OFF,
            sec_left: SEC_UPTIME,
            sec_right: SEC_LOAD,
            ..Default::default()
        };
        let b = st.pack();
        assert_eq!(u16::from_le_bytes([b[0], b[1]]), 0xABCD);
        assert_eq!(b[22], METER_OFF);
        assert_eq!(b[23], 42);
        assert_eq!(b[24], 77);
        assert_eq!(b[25], SEC_UPTIME);
        assert_eq!(b[26], SEC_LOAD);
    }

    #[test]
    fn style_pack_osd_fields() {
        let st = StatusStyle {
            osd_default_bright_pct: 4,
            osd_sleep_timeout_s: 3,
            osd_flags: OSD_F_DISMISS_ON_TAP | OSD_F_AUTO_BRIGHT,
            osd_auto_day_pct: 5,
            osd_auto_night_pct: 2,
            osd_auto_day_hour: 6,
            osd_auto_night_hour: 22,
            ..Default::default()
        };
        let b = st.pack();
        let o = STYLE_LEN - 8;
        assert_eq!(b[o], 4);
        assert_eq!(u16::from_le_bytes([b[o + 1], b[o + 2]]), 3);
        assert_eq!(b[o + 3], OSD_F_DISMISS_ON_TAP | OSD_F_AUTO_BRIGHT);
        assert_eq!(b[o + 4], 5);
        assert_eq!(b[o + 5], 2);
        assert_eq!(b[o + 6], 6);
        assert_eq!(b[o + 7], 22);
    }

    #[test]
    fn snap_pack_magic_ver_and_fields() {
        let mut snap = StatusSnap {
            flags: ST_F_HAS_CPU | ST_F_HAS_MEM,
            hostname: "host-xyz".into(),
            date: "08-09-2026".into(),
            time: "15:04:05".into(),
            load_x100: [123, 456, 789],
            uptime_sec: 0x11223344,
            cpu_pct: 10,
            mem_pct: 20,
            disk_pct: 30,
            swap_pct: 40,
            cpu_temp_c10: -150,
            ..Default::default()
        };
        snap.ifaces.push(StatusIface {
            name: "eth0".into(),
            ip: "10.0.0.1".into(),
            rx_bps: 100,
            tx_bps: 200,
        });
        snap.services.push(StatusSvc {
            name: "ssh".into(),
            status: ST_SVC_ACTIVE,
        });
        snap.services.push(StatusSvc {
            name: "x".repeat(SVC_NAME_LEN + 5),
            status: ST_SVC_FAILED,
        });

        let packed = snap.pack();
        assert_eq!(&packed[0..4], b"TBST");
        assert_eq!(packed[4], STATUS_VER);
        assert_eq!(packed[5], ST_F_HAS_CPU | ST_F_HAS_MEM);

        let style_end = 6 + STYLE_LEN;
        let host = &packed[style_end..style_end + 24];
        assert_eq!(&host[..8], b"host-xyz");
        assert!(host[8..].iter().all(|&c| c == 0));

        let date_off = style_end + 24;
        assert_eq!(&packed[date_off..date_off + 10], b"08-09-2026");
        let time_off = date_off + 20;
        assert_eq!(&packed[time_off..time_off + 8], b"15:04:05");

        let load_off = time_off + 12;
        assert_eq!(
            u16::from_le_bytes([packed[load_off], packed[load_off + 1]]),
            123
        );
        assert_eq!(
            u16::from_le_bytes([packed[load_off + 2], packed[load_off + 3]]),
            456
        );

        let up_off = load_off + 6;
        assert_eq!(
            u32::from_le_bytes(packed[up_off..up_off + 4].try_into().unwrap()),
            0x11223344
        );
        assert_eq!(&packed[up_off + 4..up_off + 8], &[10u8, 20, 30, 40]);

        let payload = snap.to_payload();
        assert_eq!(payload.len(), PAYLOAD_LEN);
        assert_eq!(&payload[..STATUS_SNAP_LEN], &packed);
        assert!(payload[STATUS_SNAP_LEN..].iter().all(|&b| b == 0));
    }

    #[test]
    fn empty_service_slot_status_is_zero() {
        let packed = StatusSnap::default().pack();
        // Services start after fixed header + 16 iface slots (64 bytes each).
        let iface_block = IFACE_COUNT * (16 + 40 + 4 + 4);
        let header = 6 + STYLE_LEN + 24 + 20 + 12 + 6 + 4 + 4 + 24 + 2;
        let svc0 = header + iface_block;
        assert_eq!(&packed[svc0..svc0 + SVC_NAME_LEN], &[0u8; SVC_NAME_LEN]);
        assert_eq!(packed[svc0 + SVC_NAME_LEN], 0);
    }

    #[test]
    fn wire_constants_match_firmware() {
        // Keep in lockstep with firmware/src/protocol.h + status_snap.h.
        assert_eq!(FRAME_MAGIC, [0xAA, 0x55, 0xA5, 0x5A]);
        assert_eq!(FRAME_ACK, 0x06);
        assert_eq!(FRAME_NAK, 0x15);
        assert_eq!(DEV_MODE_TOGGLE, 0x12);
        assert_eq!(DEV_OSD_BRIGHT, 0x13);
        assert_eq!(DEV_OSD_SLEEP, 0x14);
        assert_eq!(FLAG_CURSOR_VISIBLE, 0x01);
        assert_eq!(FLAG_CURSOR_ON, 0x02);
        assert_eq!(FLAG_ACTIVITY, 0x04);
        assert_eq!(FLAG_STYLE, 0x10);
        assert_eq!(FLAG_STATUS, 0x20);
        assert_eq!(FLAG_BYE, 0x80);
        assert_eq!(COLS, 53);
        assert_eq!(ROWS, 30);
        assert_eq!(PAYLOAD_LEN, 4770);
        assert_eq!(FRAME_LEN, 4780);
        assert_eq!(STATUS_VER, 13);
        assert_eq!(STATUS_SNAP_LEN, 4466);
        assert_eq!(STYLE_LEN, 60);
        assert_eq!(IFACE_COUNT, 16);
        assert_eq!(SVC_COUNT, 80);
        assert_eq!(SVC_NAME_LEN, 40);
        assert_eq!(ST_F_HAS_TEMP, 0x02);
        assert_eq!(ST_F_HAS_CPU, 0x20);
        assert_eq!(ST_F_HAS_MEM, 0x40);
        assert_eq!(ST_F_HAS_DISK, 0x80);
        assert_eq!(
            [
                ST_SVC_FAILED,
                ST_SVC_ACTIVE,
                ST_SVC_DEACTIVATING,
                ST_SVC_ACTIVATING,
                ST_SVC_INACTIVE,
                ST_SVC_MAINTENANCE,
                ST_SVC_RELOADING
            ],
            [0, 1, 2, 3, 4, 5, 6]
        );
        assert_eq!(SEC_NONE, 0xFF);
        assert_eq!([SEC_UPTIME, SEC_SWAP, SEC_LOAD], [1, 2, 3]);
        assert_eq!(
            [
                AL_CPU,
                AL_MEM,
                AL_DISK,
                AL_TEMP,
                AL_SVC_FAILED,
                AL_SVC_INACTIVE
            ],
            [1, 2, 4, 8, 16, 32]
        );
        assert_eq!(
            [OSD_F_DISMISS_ON_TAP, OSD_F_AUTO_BRIGHT, OSD_F_WAKE_ON_ALERT],
            [1, 2, 4]
        );
    }

    /// Shared byte layout with firmware `test_status_style_pack_golden`.
    fn golden_style() -> StatusStyle {
        StatusStyle {
            label_c: 0x1111,
            bg_c: 0x2222,
            host_c: 0x3333,
            date_c: 0x4444,
            time_c: 0x5555,
            level_ok: 0x6666,
            level_warn: 0x7777,
            level_crit: 0x8888,
            hero_cpu_c: 0x9999,
            hero_mem_c: 0xAAAA,
            hero_disk_c: 0xBBBB,
            meter_mode: METER_ON,
            warn_at: 60,
            crit_at: 90,
            sec_left: SEC_UPTIME,
            sec_right: SEC_LOAD,
            sec_left_c: 0xCCCC,
            sec_right_c: 0xDDDD,
            svc_active: 0x0101,
            svc_failed: 0x0202,
            svc_deactivating: 0x0303,
            svc_activating: 0x0404,
            svc_reloading: 0x0505,
            svc_inactive: 0x0606,
            svc_maintenance: 0x0707,
            alert_bg_c: 0x0808,
            alert_fg_c: 0x0909,
            alert_hold_sec: 30,
            alert_mask: 0x3F,
            alert_temp_c: 80,
            osd_default_bright_pct: 4,
            osd_sleep_timeout_s: 4,
            osd_flags: OSD_F_DISMISS_ON_TAP | OSD_F_WAKE_ON_ALERT,
            osd_auto_day_pct: 5,
            osd_auto_night_pct: 2,
            osd_auto_day_hour: 7,
            osd_auto_night_hour: 21,
        }
    }

    #[test]
    fn status_style_pack_golden() {
        const GOLDEN: [u8; STYLE_LEN] = [
            0x11, 0x11, 0x22, 0x22, 0x33, 0x33, 0x44, 0x44, 0x55, 0x55, 0x66, 0x66, 0x77, 0x77,
            0x88, 0x88, 0x99, 0x99, 0xAA, 0xAA, 0xBB, 0xBB, 0x01, 0x3C, 0x5A, 0x01, 0x03, 0xCC,
            0xCC, 0xDD, 0xDD, 0x01, 0x01, 0x02, 0x02, 0x03, 0x03, 0x04, 0x04, 0x05, 0x05, 0x06,
            0x06, 0x07, 0x07, 0x08, 0x08, 0x09, 0x09, 0x1E, 0x3F, 0x50, 0x04, 0x04, 0x00, 0x05,
            0x05, 0x02, 0x07, 0x15,
        ];
        assert_eq!(golden_style().pack(), GOLDEN);
    }

    #[test]
    fn status_snap_header_golden() {
        let mut snap = StatusSnap {
            flags: ST_F_HAS_CPU | ST_F_HAS_MEM | ST_F_HAS_DISK,
            style: golden_style(),
            hostname: "buddy".into(),
            date: "09-09-2026".into(),
            time: "12:00:00".into(),
            load_x100: [100, 200, 300],
            uptime_sec: 3600,
            cpu_pct: 11,
            mem_pct: 22,
            disk_pct: 33,
            swap_pct: 44,
            mem_used_mb: 1024,
            mem_total_mb: 2048,
            disk_used_mb: 4096,
            disk_total_mb: 8192,
            swap_used_mb: 1,
            swap_total_mb: 2,
            cpu_temp_c10: 425,
            ..Default::default()
        };
        snap.ifaces.push(StatusIface {
            name: "eth0".into(),
            ip: "10.0.0.1".into(),
            rx_bps: 1000,
            tx_bps: 2000,
        });
        snap.services.push(StatusSvc {
            name: "ssh".into(),
            status: ST_SVC_ACTIVE,
        });

        let packed = snap.pack();
        assert_eq!(&packed[0..4], b"TBST");
        assert_eq!(packed[4], STATUS_VER);
        assert_eq!(packed[5], ST_F_HAS_CPU | ST_F_HAS_MEM | ST_F_HAS_DISK);
        assert_eq!(&packed[6..6 + STYLE_LEN], &golden_style().pack());

        let style_end = 6 + STYLE_LEN;
        assert_eq!(&packed[style_end..style_end + 5], b"buddy");
        assert!(packed[style_end + 5..style_end + 24]
            .iter()
            .all(|&b| b == 0));

        let date_off = style_end + 24;
        assert_eq!(&packed[date_off..date_off + 10], b"09-09-2026");
        let time_off = date_off + 20;
        assert_eq!(&packed[time_off..time_off + 8], b"12:00:00");

        let load_off = time_off + 12;
        assert_eq!(
            u16::from_le_bytes([packed[load_off], packed[load_off + 1]]),
            100
        );
        let up_off = load_off + 6;
        assert_eq!(
            u32::from_le_bytes(packed[up_off..up_off + 4].try_into().unwrap()),
            3600
        );
        assert_eq!(&packed[up_off + 4..up_off + 8], &[11u8, 22, 33, 44]);

        let mem_off = up_off + 8;
        assert_eq!(
            u32::from_le_bytes(packed[mem_off..mem_off + 4].try_into().unwrap()),
            1024
        );

        let iface0 = 6 + STYLE_LEN + 24 + 20 + 12 + 6 + 4 + 4 + 24 + 2;
        assert_eq!(&packed[iface0..iface0 + 4], b"eth0");
        assert_eq!(&packed[iface0 + 16..iface0 + 24], b"10.0.0.1");
        assert_eq!(
            u32::from_le_bytes(packed[iface0 + 56..iface0 + 60].try_into().unwrap()),
            1000
        );
        assert_eq!(
            u32::from_le_bytes(packed[iface0 + 60..iface0 + 64].try_into().unwrap()),
            2000
        );

        let svc0 = iface0 + IFACE_COUNT * 64;
        assert_eq!(&packed[svc0..svc0 + 3], b"ssh");
        assert_eq!(packed[svc0 + SVC_NAME_LEN], ST_SVC_ACTIVE);
    }

    #[test]
    fn status_frame_crc_golden() {
        let payload = [0u8; PAYLOAD_LEN];
        let frame = build_frame(1, 0, 0, FLAG_STATUS | FLAG_STYLE, &payload);
        assert_eq!(frame.len(), FRAME_LEN);
        assert_eq!(&frame[0..4], &FRAME_MAGIC);
        assert_eq!(frame[7], FLAG_STATUS | FLAG_STYLE);
        let mut crc_buf = vec![1u8, 0, 0, FLAG_STATUS | FLAG_STYLE];
        crc_buf.extend_from_slice(&payload);
        let crc = crc16_ccitt(&crc_buf);
        assert_eq!(frame[FRAME_LEN - 2], (crc >> 8) as u8);
        assert_eq!(frame[FRAME_LEN - 1], (crc & 0xFF) as u8);
        // CRC over hdr+empty payload; must match firmware `test_status_frame_crc_golden`.
        assert_eq!(crc, 0x9D4D);
    }
}
