imflawlezz/tty-buddy/firmware/src/osd.h

#pragma once

#include <Arduino.h>
#include <TFT_eSPI.h>

#include "terminal.h"

// Button OSD, backlight PWM, and inactivity sleep/wake.
namespace osd {

void begin(TFT_eSPI *tft, Terminal *term);
void tick(uint32_t now);
/** Dirty-row redraw; call after content paint so wipes can be restored. */
void paint();

/** Reset sleep timer and wake if asleep (host keyboard / FLAG_ACTIVITY). */
void noteActivity(uint32_t now);

bool isOpen();
bool isAsleep();

} // namespace osd
