imflawlezz/tty-buddy/daemon/src/lib.rs

//! Shared library for the tty-buddy host daemon.

pub mod bridge;
pub mod discover;
pub mod keyboard;
pub mod metrics;
pub mod protocol;
pub mod serial_io;
pub mod settings;
pub mod status_config;
pub mod terminal;
