imflawlezz/tty-buddy/firmware/src/protocol.cpp

#include "protocol.h"

uint16_t crc16_ccitt(const uint8_t *data, size_t n, uint16_t seed) {
  uint16_t crc = seed;
  for (size_t i = 0; i < n; i++) {
    crc ^= (uint16_t)data[i] << 8;
    for (int b = 0; b < 8; b++)
      crc = (crc & 0x8000) ? (uint16_t)((crc << 1) ^ 0x1021) : (uint16_t)(crc << 1);
  }
  return crc;
}
